cuu508/co2sensor/Lato.h

const uint8_t Lato_Black50pt7bBitmaps[] PROGMEM = {
  0x00, 0x00, 0x07, 0xFF, 0x00, 0x00, 0x00, 0x00, 0x01, 0xFF, 0xFF, 0x00,
  0x00, 0x00, 0x00, 0x7F, 0xFF, 0xFF, 0x00, 0x00, 0x00, 0x0F, 0xFF, 0xFF,
  0xFC, 0x00, 0x00, 0x00, 0xFF, 0xFF, 0xFF, 0xF8, 0x00, 0x00, 0x0F, 0xFF,
  0xFF, 0xFF, 0xE0, 0x00, 0x00, 0xFF, 0xFF, 0xFF, 0xFF, 0x80, 0x00, 0x0F,
  0xFF, 0xFF, 0xFF, 0xFE, 0x00, 0x00, 0xFF, 0xFF, 0xFF, 0xFF, 0xF8, 0x00,
  0x0F, 0xFF, 0xFF, 0xFF, 0xFF, 0xE0, 0x00, 0xFF, 0xFF, 0xFF, 0xFF, 0xFF,
  0x00, 0x07, 0xFF, 0xFF, 0xFF, 0xFF, 0xFC, 0x00, 0x7F, 0xFF, 0xF0, 0x7F,
  0xFF, 0xF0, 0x03, 0xFF, 0xFE, 0x00, 0xFF, 0xFF, 0x80, 0x3F, 0xFF, 0xE0,
  0x03, 0xFF, 0xFE, 0x01, 0xFF, 0xFE, 0x00, 0x0F, 0xFF, 0xF0, 0x1F, 0xFF,
  0xE0, 0x00, 0x3F, 0xFF, 0xC0, 0xFF, 0xFF, 0x00, 0x01, 0xFF, 0xFE, 0x0F,
  0xFF, 0xF0, 0x00, 0x07, 0xFF, 0xF0, 0x7F, 0xFF, 0x80, 0x00, 0x3F, 0xFF,
  0xC3, 0xFF, 0xF8, 0x00, 0x01, 0xFF, 0xFE, 0x1F, 0xFF, 0xC0, 0x00, 0x07,
  0xFF, 0xF1, 0xFF, 0xFE, 0x00, 0x00, 0x3F, 0xFF, 0x8F, 0xFF, 0xF0, 0x00,
  0x01, 0xFF, 0xFE, 0x7F, 0xFF, 0x80, 0x00, 0x0F, 0xFF, 0xF3, 0xFF, 0xF8,
  0x00, 0x00, 0x7F, 0xFF, 0x9F, 0xFF, 0xC0, 0x00, 0x01, 0xFF, 0xFD, 0xFF,
  0xFE, 0x00, 0x00, 0x0F, 0xFF, 0xEF, 0xFF, 0xF0, 0x00, 0x00, 0x7F, 0xFF,
  0x7F, 0xFF, 0x80, 0x00, 0x03, 0xFF, 0xFF, 0xFF, 0xFC, 0x00, 0x00, 0x1F,
  0xFF, 0xFF, 0xFF, 0xE0, 0x00, 0x00, 0xFF, 0xFF, 0xFF, 0xFF, 0x00, 0x00,
  0x07, 0xFF, 0xFF, 0xFF, 0xF8, 0x00, 0x00, 0x3F, 0xFF, 0xFF, 0xFF, 0xC0,
  0x00, 0x01, 0xFF, 0xFF, 0xFF, 0xFE, 0x00, 0x00, 0x0F, 0xFF, 0xFF, 0xFF,
  0xF0, 0x00, 0x00, 0x7F, 0xFF, 0xFF, 0xFF, 0x80, 0x00, 0x03, 0xFF, 0xFF,
  0xFF, 0xFC, 0x00, 0x00, 0x1F, 0xFF, 0xFF, 0xFF, 0xE0, 0x00, 0x00, 0xFF,
  0xFF, 0xFF, 0xFF, 0x00, 0x00, 0x07, 0xFF, 0xFF, 0xFF, 0xF8, 0x00, 0x00,
  0x3F, 0xFF, 0xFF, 0xFF, 0xC0, 0x00, 0x01, 0xFF, 0xFF, 0xFF, 0xFE, 0x00,
  0x00, 0x0F, 0xFF, 0xFF, 0xFF, 0xF0, 0x00, 0x00, 0x7F, 0xFF, 0x7F, 0xFF,
  0x80, 0x00, 0x03, 0xFF, 0xF9, 0xFF, 0xFC, 0x00, 0x00, 0x1F, 0xFF, 0xCF,
  0xFF, 0xE0, 0x00, 0x01, 0xFF, 0xFE, 0x7F, 0xFF, 0x80, 0x00, 0x0F, 0xFF,
  0xF3, 0xFF, 0xFC, 0x00, 0x00, 0x7F, 0xFF, 0x9F, 0xFF, 0xE0, 0x00, 0x03,
  0xFF, 0xF8, 0x7F, 0xFF, 0x00, 0x00, 0x1F, 0xFF, 0xC3, 0xFF, 0xF8, 0x00,
  0x01, 0xFF, 0xFE, 0x1F, 0xFF, 0xE0, 0x00, 0x0F, 0xFF, 0xF0, 0xFF, 0xFF,
  0x00, 0x00, 0x7F, 0xFF, 0x03, 0xFF, 0xFC, 0x00, 0x07, 0xFF, 0xF8, 0x1F,
  0xFF, 0xE0, 0x00, 0x3F, 0xFF, 0xC0, 0x7F, 0xFF, 0x80, 0x03, 0xFF, 0xFC,
  0x03, 0xFF, 0xFE, 0x00, 0x3F, 0xFF, 0xE0, 0x0F, 0xFF, 0xF8, 0x03, 0xFF,
  0xFE, 0x00, 0x7F, 0xFF, 0xF0, 0x7F, 0xFF, 0xF0, 0x01, 0xFF, 0xFF, 0xFF,
  0xFF, 0xFF, 0x00, 0x0F, 0xFF, 0xFF, 0xFF, 0xFF, 0xF0, 0x00, 0x3F, 0xFF,
  0xFF, 0xFF, 0xFF, 0x80, 0x00, 0xFF, 0xFF, 0xFF, 0xFF, 0xF8, 0x00, 0x03,
  0xFF, 0xFF, 0xFF, 0xFF, 0x80, 0x00, 0x0F, 0xFF, 0xFF, 0xFF, 0xF8, 0x00,
  0x00, 0x3F, 0xFF, 0xFF, 0xFF, 0x80, 0x00, 0x00, 0xFF, 0xFF, 0xFF, 0xF8,
  0x00, 0x00, 0x03, 0xFF, 0xFF, 0xFF, 0x00, 0x00, 0x00, 0x07, 0xFF, 0xFF,
  0xE0, 0x00, 0x00, 0x00, 0x07, 0xFF, 0xFC, 0x00, 0x00, 0x00, 0x00, 0x07,
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

const GFXglyph Lato_Black50pt7bGlyphs[] PROGMEM = {
  {     0,  53,  73,  57,    2,  -71 },   // 0x30 '0'
  {   484,  47,  72,  57,    6,  -71 },   // 0x31 '1'
  {   907,  50,  72,  57,    3,  -71 },   // 0x32 '2'
  {  1357,  50,  73,  57,    4,  -71 },   // 0x33 '3'
  {  1814,  55,  73,  57,    0,  -72 },   // 0x34 '4'
  {  2316,  50,  73,  57,    2,  -71 },   // 0x35 '5'
  {  2773,  52,  73,  57,    3,  -71 },   // 0x36 '6'
  {  3248,  50,  72,  57,    4,  -71 },   // 0x37 '7'
  {  3698,  51,  73,  57,    3,  -71 },   // 0x38 '8'
  {  4164,  50,  73,  57,    5,  -72 } }; // 0x39 '9'

const GFXfont Lato_Black50pt7b PROGMEM = {
  (uint8_t  *)Lato_Black50pt7bBitmaps,
  (GFXglyph *)Lato_Black50pt7bGlyphs,
  0x30, 0x39, 118 };

// Approx. 4698 bytes
