cuu508/co2sensor/pf.h

const uint8_t pf_tempesta_seven4pt7bBitmaps[] PROGMEM = {
  0x74, 0x63, 0x18, 0xC5, 0xC0, 0xD5, 0x54, 0xF0, 0x42, 0xE8, 0x43, 0xE0,
  0xF0, 0x42, 0xE0, 0x87, 0xC0, 0x32, 0x95, 0x2F, 0x88, 0x40, 0xFC, 0x21,
  0xE0, 0x87, 0xC0, 0x74, 0x21, 0xE8, 0xC5, 0xC0, 0xF8, 0x44, 0x22, 0x11,
  0x00, 0x74, 0x62, 0xE8, 0xC5, 0xC0, 0x74, 0x62, 0xF0, 0x85, 0xC0 };

const GFXglyph pf_tempesta_seven4pt7bGlyphs[] PROGMEM = {
  {     0,   5,   7,   6,    0,   -6 },   // 0x30 '0'
  {     5,   2,   7,   3,    0,   -6 },   // 0x31 '1'
  {     7,   5,   7,   6,    0,   -6 },   // 0x32 '2'
  {    12,   5,   7,   6,    0,   -6 },   // 0x33 '3'
  {    17,   5,   7,   6,    0,   -6 },   // 0x34 '4'
  {    22,   5,   7,   6,    0,   -6 },   // 0x35 '5'
  {    27,   5,   7,   6,    0,   -6 },   // 0x36 '6'
  {    32,   5,   7,   6,    0,   -6 },   // 0x37 '7'
  {    37,   5,   7,   6,    0,   -6 },   // 0x38 '8'
  {    42,   5,   7,   6,    0,   -6 } }; // 0x39 '9'

const GFXfont pf_tempesta_seven4pt7b PROGMEM = {
  (uint8_t  *)pf_tempesta_seven4pt7bBitmaps,
  (GFXglyph *)pf_tempesta_seven4pt7bGlyphs,
  0x30, 0x39, 13 };

// Approx. 124 bytes
